MadlyFX/OpenLUX-LED-Video-Light/Images/IMG_1346.jpg

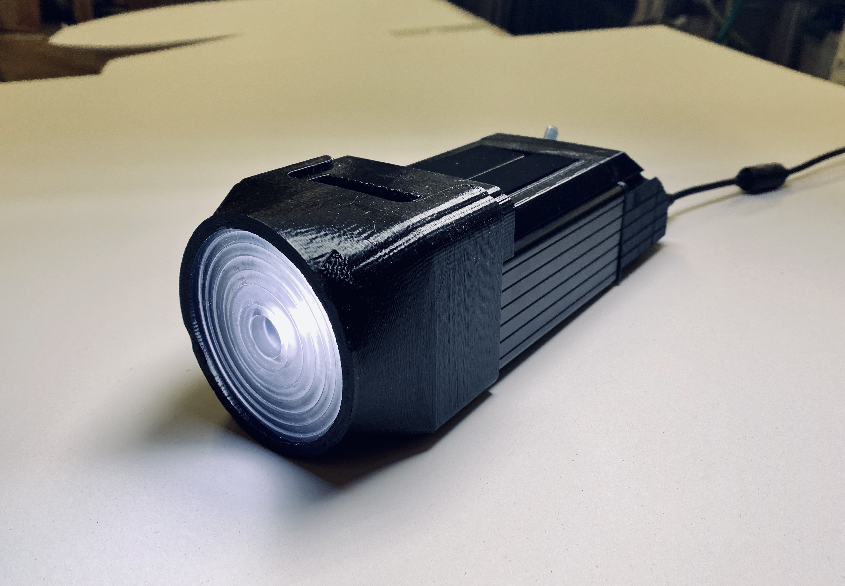
Images/IMG_1346.jpg
