MadlyFX/OpenLUX-LED-Video-Light/Images/IMG_1357.jpg

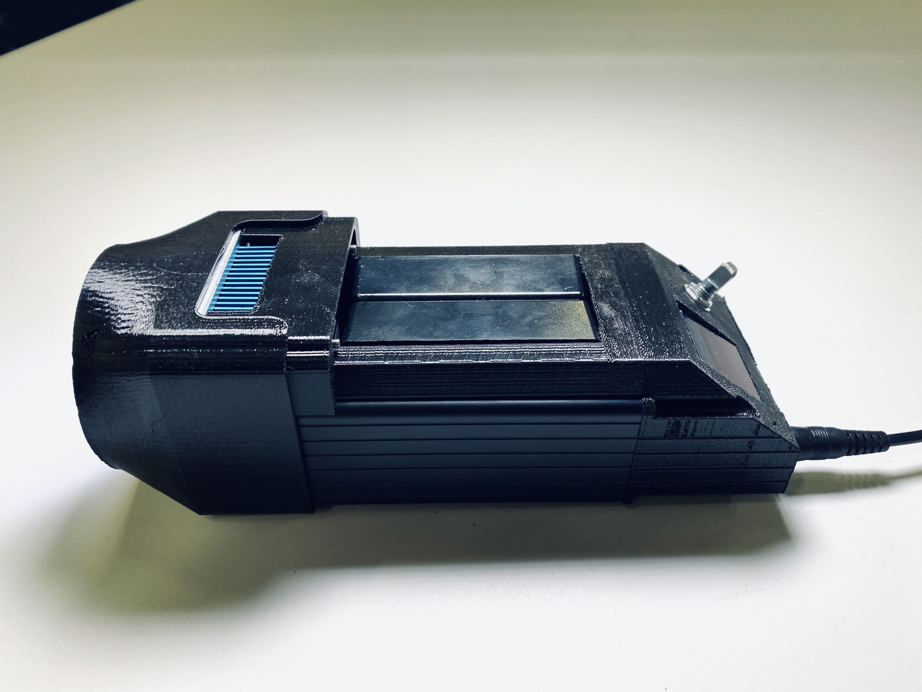
Images/IMG_1357.jpg
