MadlyFX/OpenLUX-LED-Video-Light/Images/IMG_1359.jpg

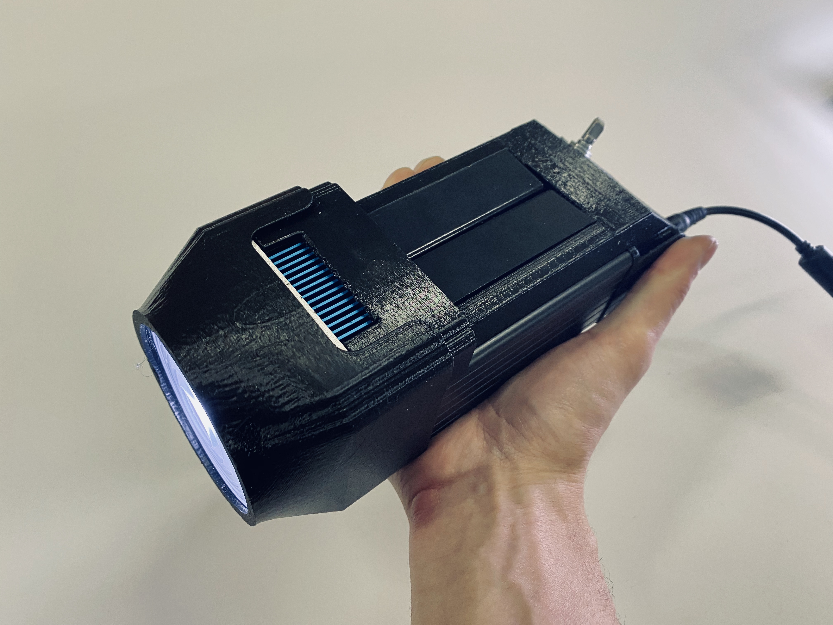
Images/IMG_1359.jpg
